mathisschmieder/HL2-MRF101/measurements/10m_RL.png

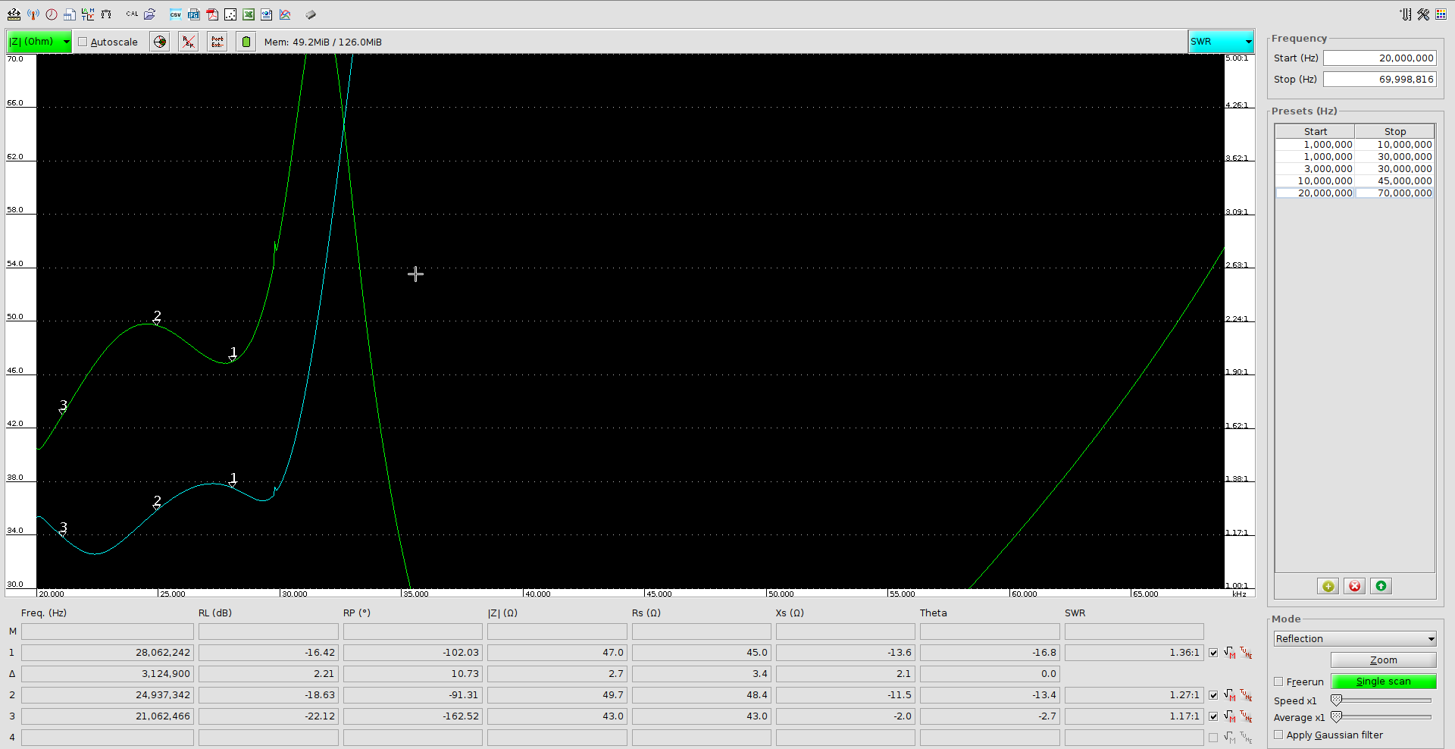
measurements/10m_RL.png
