mathisschmieder/HL2-MRF101/measurements/20m_TL.png

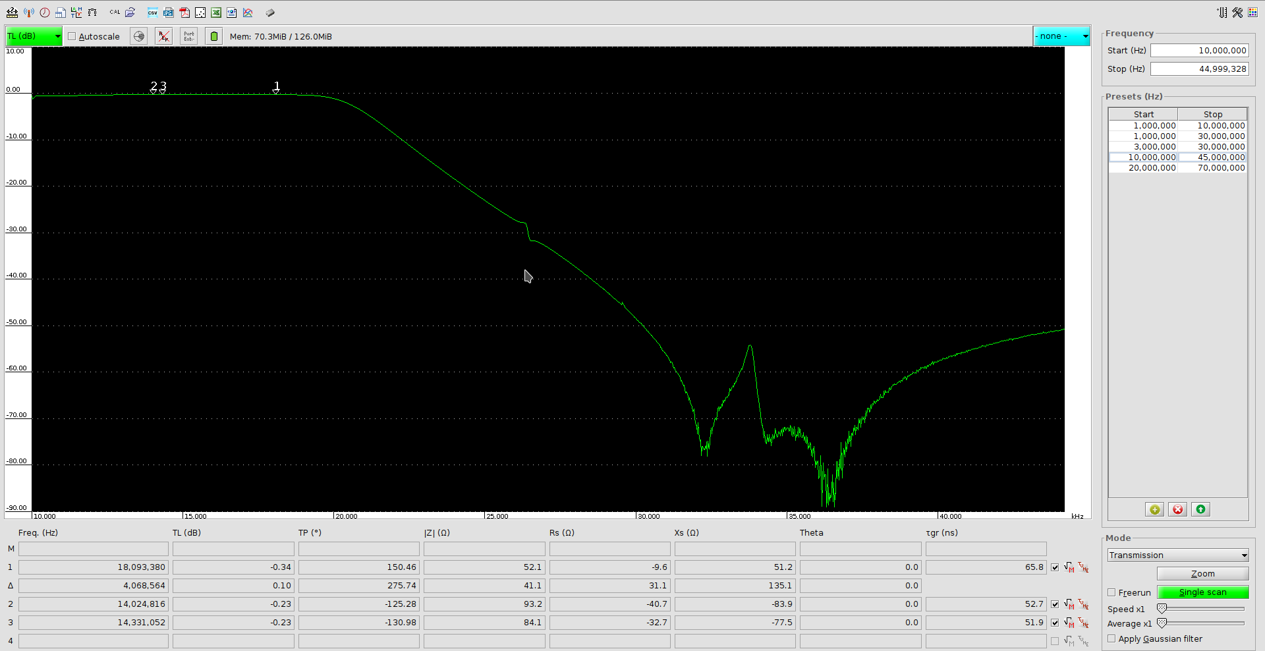
measurements/20m_TL.png
