mathisschmieder/HL2-MRF101/measurements/40m_TL.png

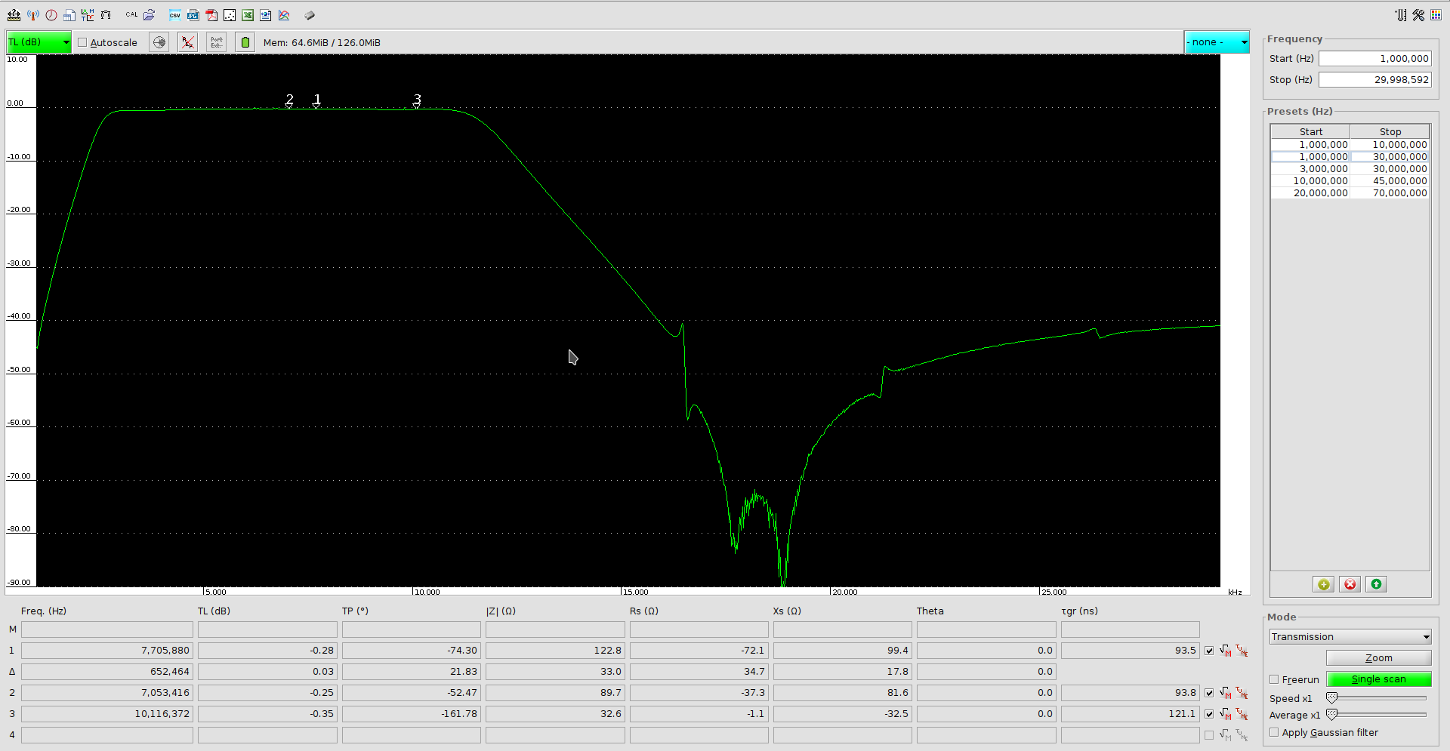
measurements/40m_TL.png
