mathisschmieder/HL2-MRF101/measurements/60m_RL.png

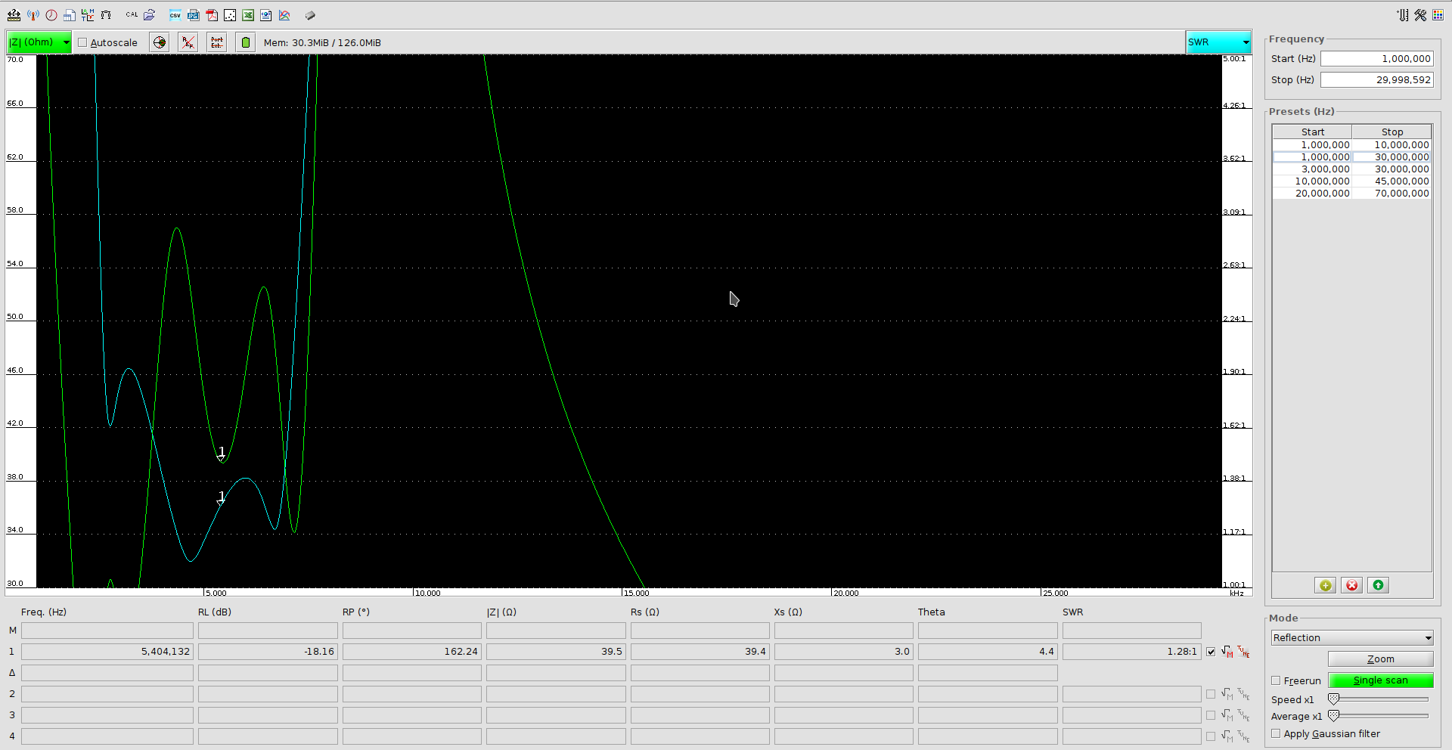
measurements/60m_RL.png
