mathisschmieder/HL2-MRF101/measurements/60m_TL.png

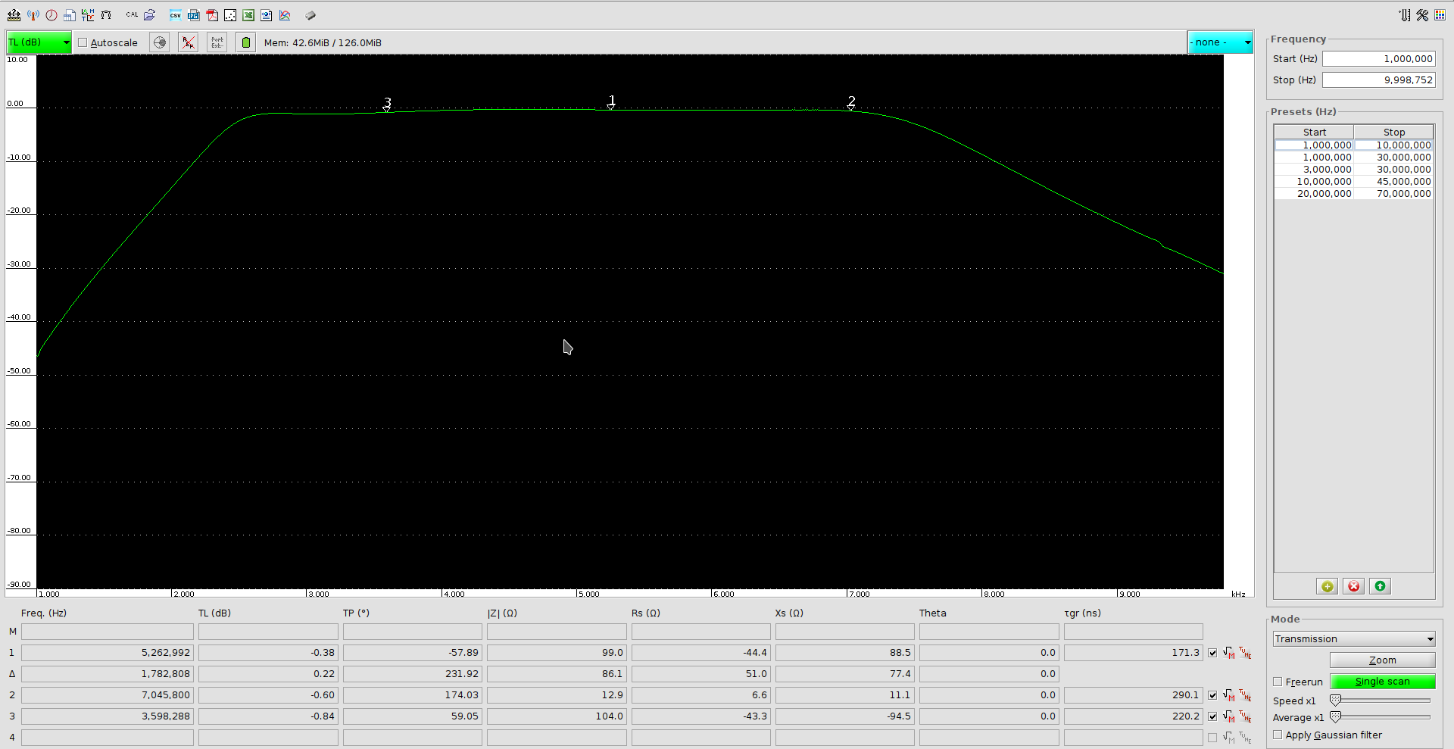
measurements/60m_TL.png
