mathisschmieder/HL2-MRF101/measurements/80m_RL.png

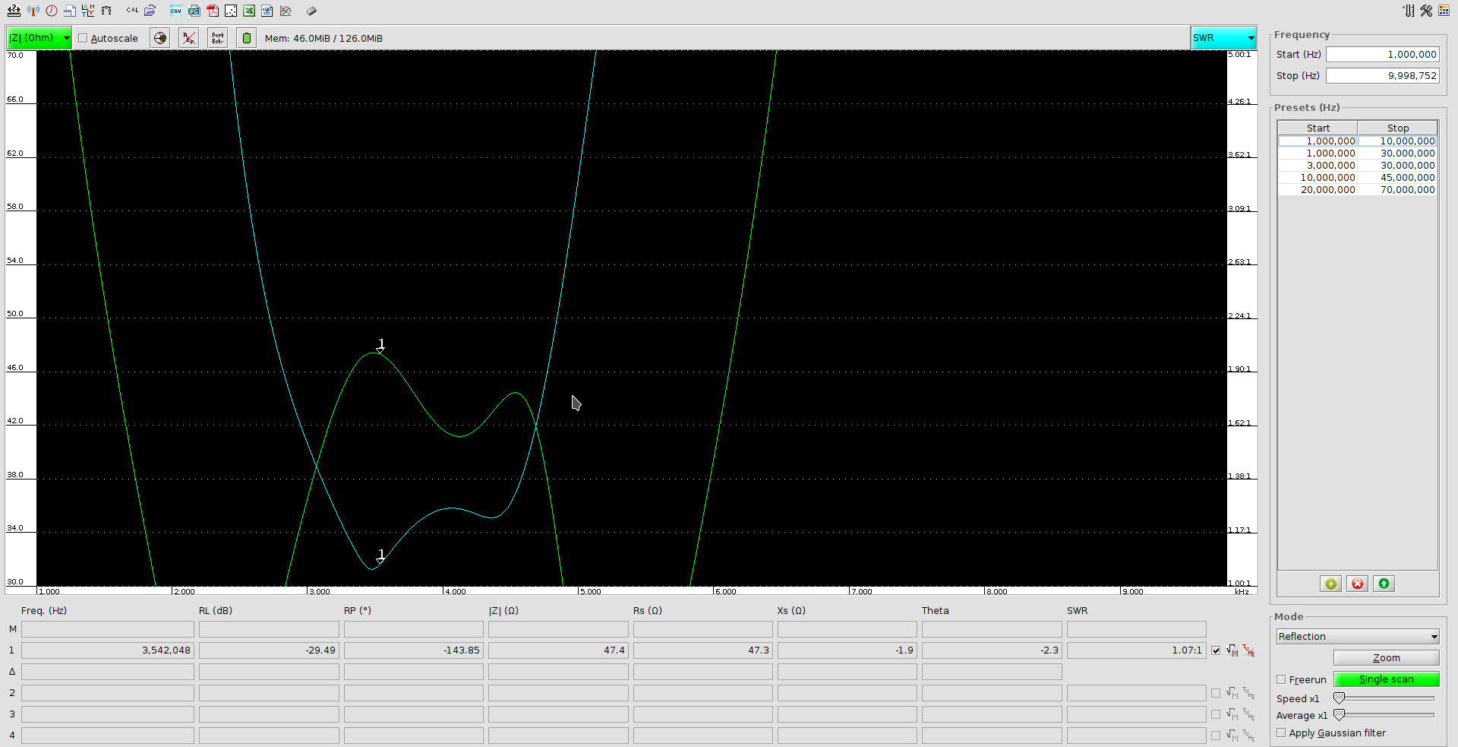
measurements/80m_RL.png
