mathisschmieder/HL2-MRF101/measurements/160m_TL.png

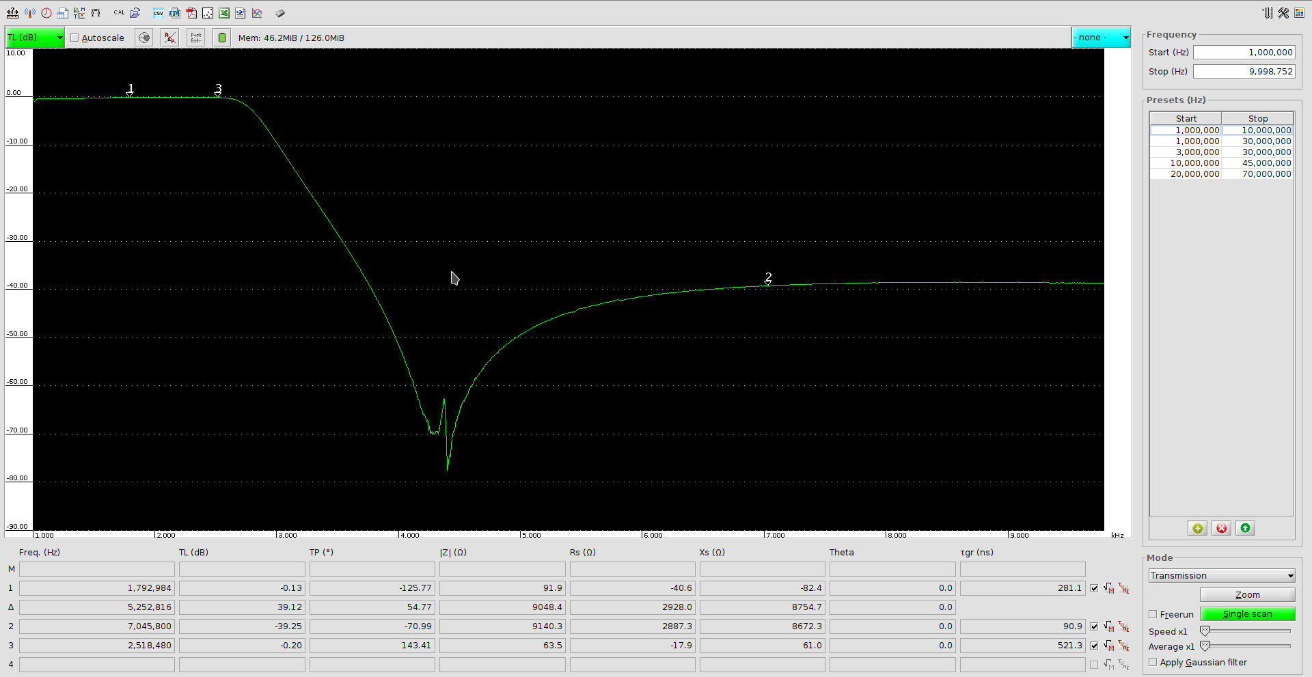
measurements/160m_TL.png
